open-batt/openbms-load-hardware/production/rev A/openbms-load-img-1.png

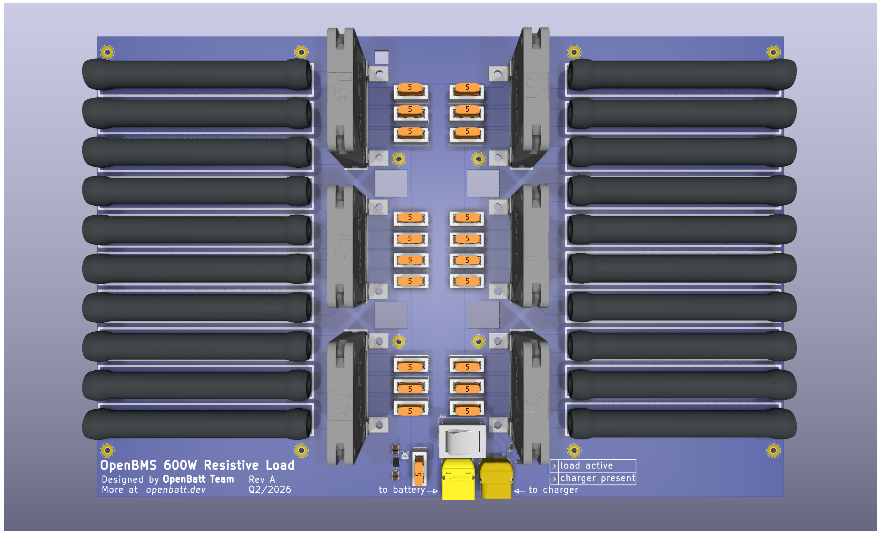
production/rev A/openbms-load-img-1.png
