open-batt/openbms-load-hardware/production/rev A/openbms-load-img-2.png

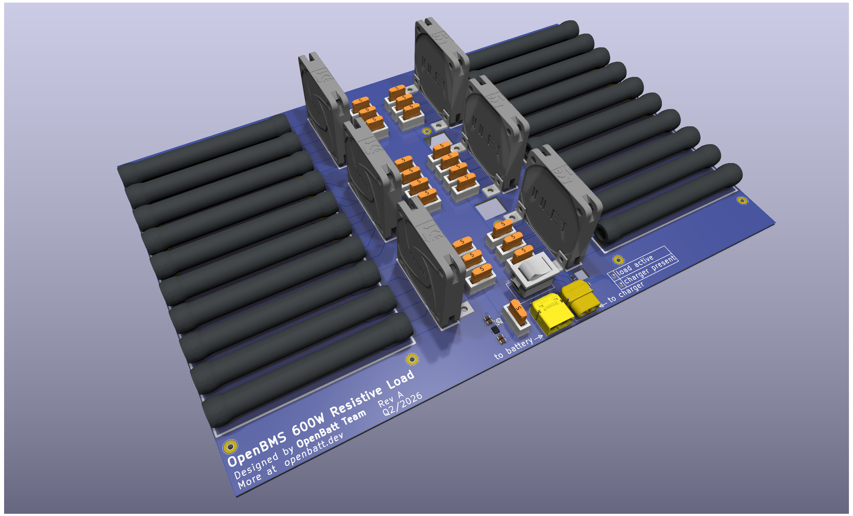
production/rev A/openbms-load-img-2.png
